jimbro1000/6847Pi/src/palette.c

#include "pico/stdlib.h"
#include "palette.h"

const int rgb_palette[PALETTE_SIZE] = {
        0,7,0, //green
        7,7,0, //yellow
        1,0,5, //blue
        5,0,1, //red
        7,7,7, //buff
        0,6,4, //cyan
        7,0,7, //magenta
        7,2,0, //orange
        0,0,0, //black
        0,2,0, //green-black
        2,1,0, //orange-black
        7,5,2, //bright-orange
};

// yab values
const int yab_palette[PALETTE_SIZE] = {
        4,0,0, //green
        3,0,1, //yellow
        5,2,1, //blue
        5,1,2, //red
        3,1,1, //buff
        4,1,1, //cyan
        4,2,2, //magenta
        4,0,2, //orange
        5,1,1, //black
        5,0,0, //green-black
        5,0,2, //orange-black
        4,0,2, //bright-orange
};

const int graphics_css0_palette[4] = {
        0,1,2,3,
};

const int graphics_css1_palette[4] = {
        4,5,6,7,
};

const int text_css0_palette[2] = {
        8,0,
};

const int text_css1_palette[2] = {
        8,11,
};

const int semi4_palette[9] = {
        8,0,1,2,3,4,5,6,7,
};

const int semi6_css0_palette[5] = {
        8,0,1,2,3,
};

const int semi6_css1_palette[5] = {
        8,4,5,6,7,
};

const int luma_css0_palette[2] = {
        8,0,
};

const int luma_css1_palette[2] = {
        8,4,
};

const int* text_palette(bool colour_set) {
    if (colour_set) {
        return text_css1_palette;
    }
    return text_css0_palette;
}

const int* semi_palette(bool colour_set) {
    if (colour_set) {
        return semi6_css1_palette;
    }
    return semi6_css0_palette;
}

const int* graphics_palette(bool colour_set) {
    if (colour_set) {
        return graphics_css1_palette;
    }
    return graphics_css0_palette;
}

const int* luma_palette(bool colour_set) {
    if (colour_set) {
        return luma_css1_palette;
    }
    return luma_css0_palette;
}

palette_t select_palette(bool colour_set, bool semigraphics, bool graphics, bool external) {
    palette_t result;
    result.source = rgb_palette;
    if (!semigraphics && !graphics) {
        result.palette_length = 2;
        result.refs = text_palette(colour_set);
    } else if (semigraphics && !external) {
        result.palette_length = 9;
        result.refs = semi4_palette;
    } else if (semigraphics) {
        result.palette_length = 5;
        result.refs = semi_palette(colour_set);
    } else {
        if (graphics % 2 == 0) {
            // colour graphics
            result.palette_length = 4;
            result.refs = graphics_palette(colour_set);
        } else {
            // luma graphics
            result.palette_length = 2;
            result.refs = luma_palette(colour_set);
        }
    }
    return result;
}
