jimbro1000/6847Pi/src/pinInterface.h

//
// Created by julian on 06/04/23.
//

#ifndef INC_6847PI_PININTERFACE_H
#define INC_6847PI_PININTERFACE_H

extern const uint32_t READ_DELAY;
extern const uint8_t EXT_PIN;
extern const uint8_t INV_PIN;
extern const uint8_t SEMI_PIN;
extern const uint8_t GRAPHICS_PIN;
extern const uint8_t COLOUR_SET;
extern const uint8_t GM0_PIN;
extern const uint8_t GM1_PIN;
extern const uint8_t GM2_PIN;
extern const uint8_t DATA_PIN_START;
extern const uint8_t DATA_PIN_COUNT;
extern const uint8_t CLOCK_PIN;
extern const uint8_t DA0_PIN;
extern const uint8_t HS_PIN;
extern const uint8_t FS_PIN;

extern const int RGB_SCALE;
extern const int RGB_PINS[];

#endif //INC_6847PI_PININTERFACE_H
