jimbro1000/6847Pi/src/vga.c

//
// Created by julian on 06/04/23.
//

const double CLOCK = 25175000L;
const double PIXEL_INTERVAL = 1/CLOCK;

const int DEFAULT_FRONT_PORCH = 16;
const int DEFAULT_SYNC = 96;
const int DEFAULT_BACK_PORCH = 48;

const int LOW_SCREEN_X = 320;
const int LOW_SCREEN_Y = 240;
const int VGA_RATIO = 2;
