jimbro1000/6847Pi/src/vga.h

//
// Created by julian on 06/04/23.
//

#ifndef INC_6847PI_VGA_H
#define INC_6847PI_VGA_H

extern const double CLOCK;
extern const double PIXEL_INTERVAL;

extern const int DEFAULT_FRONT_PORCH;
extern const int DEFAULT_SYNC;
extern const int DEFAULT_BACK_PORCH;

extern const int LOW_SCREEN_X;
extern const int LOW_SCREEN_Y;
extern const int VGA_RATIO;

#endif //INC_6847PI_VGA_H
